DigitalIdeationHSLU/DI8bitbox/documentation/EagleDXFImport.png

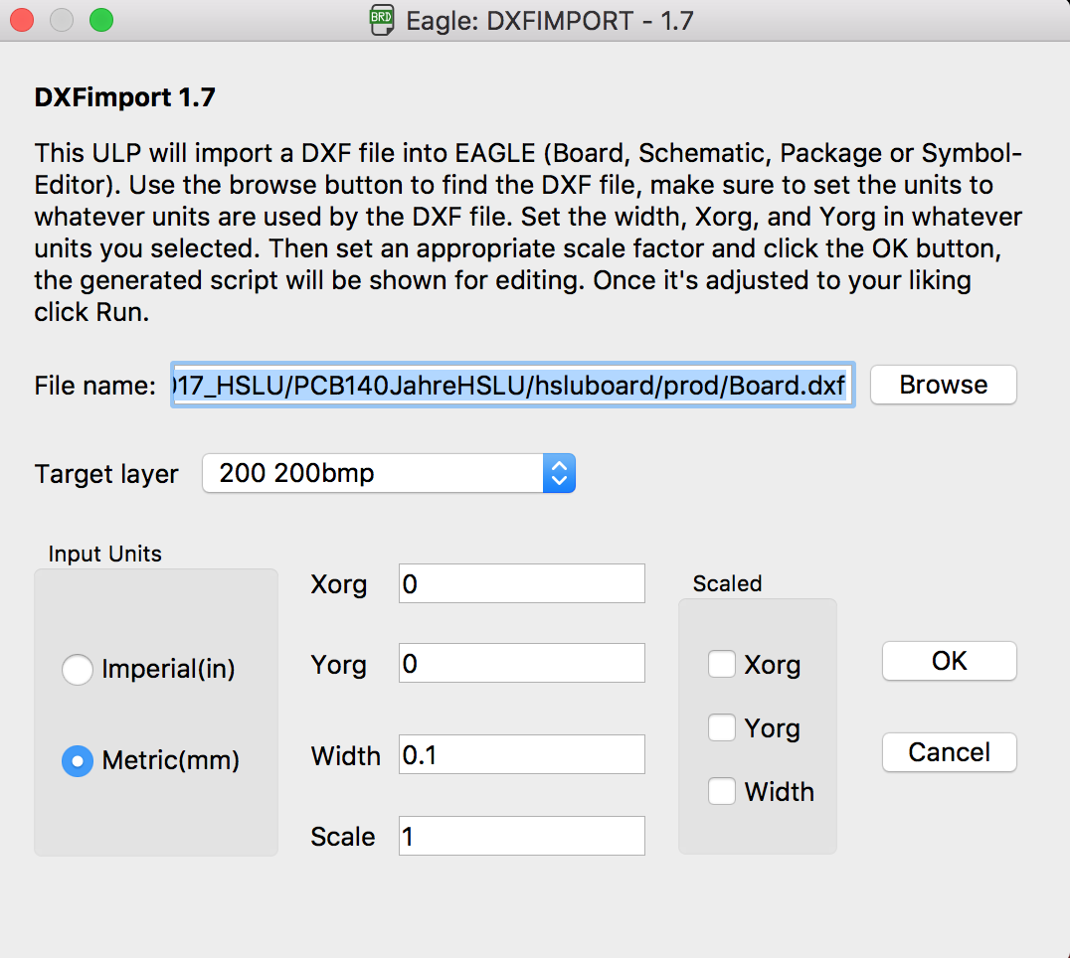
documentation/EagleDXFImport.png
