DigitalIdeationHSLU/DI8bitbox/documentation/EagleUp1.png

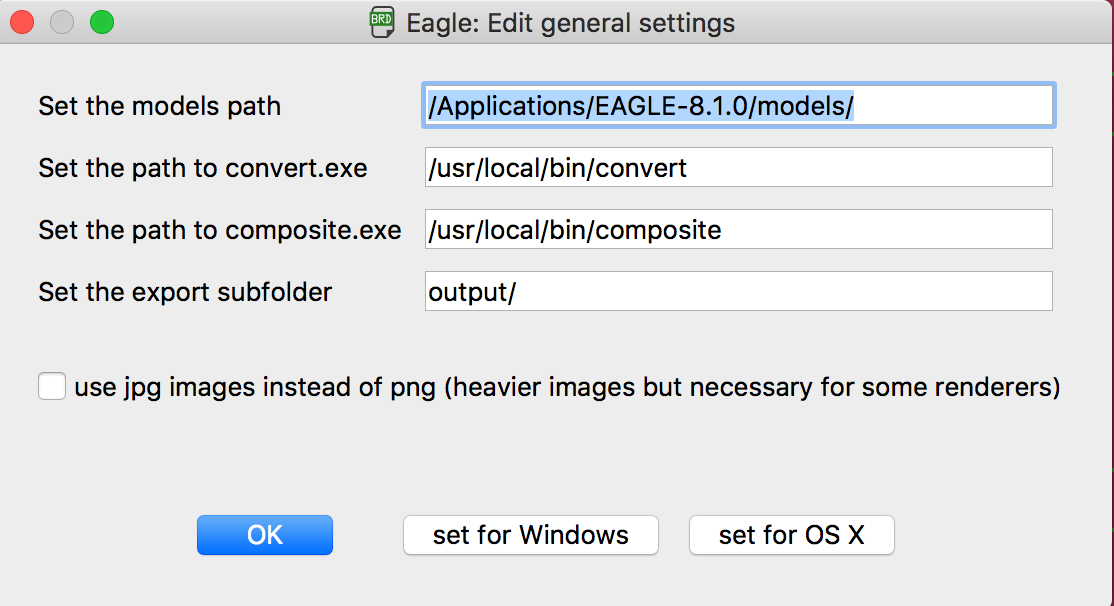
documentation/EagleUp1.png
