DigitalIdeationHSLU/DI8bitbox/documentation/EagleUp2.png

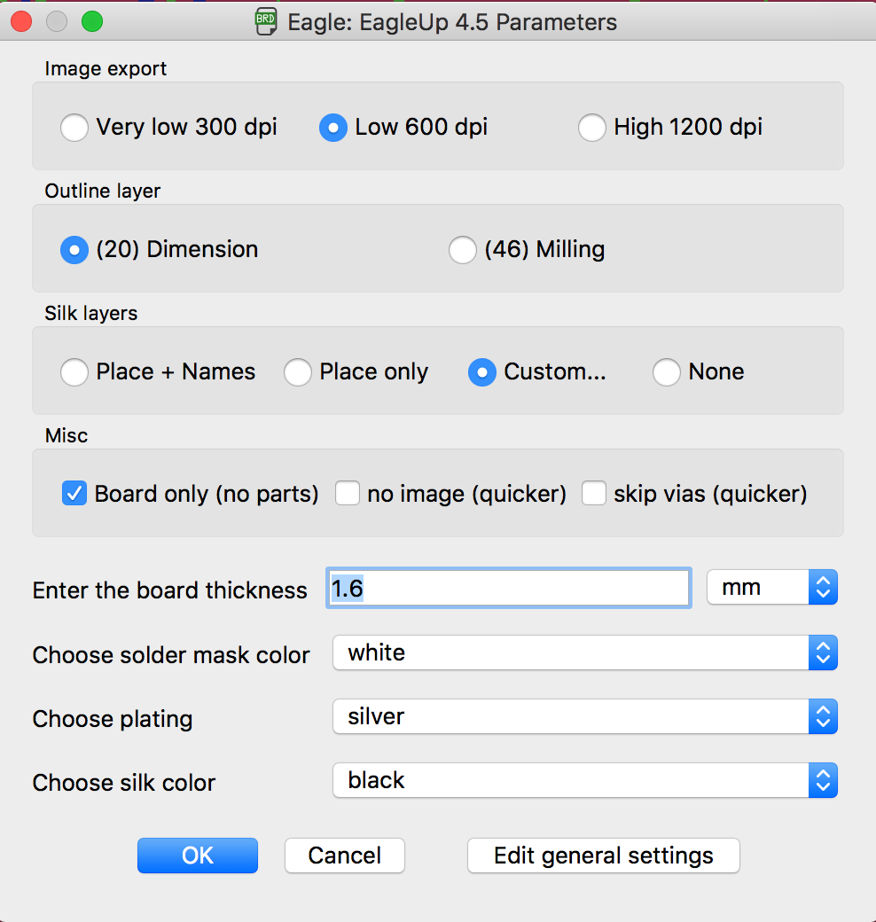
documentation/EagleUp2.png
