DigitalIdeationHSLU/DI8bitbox/documentation/IllustratorDXFexport.png

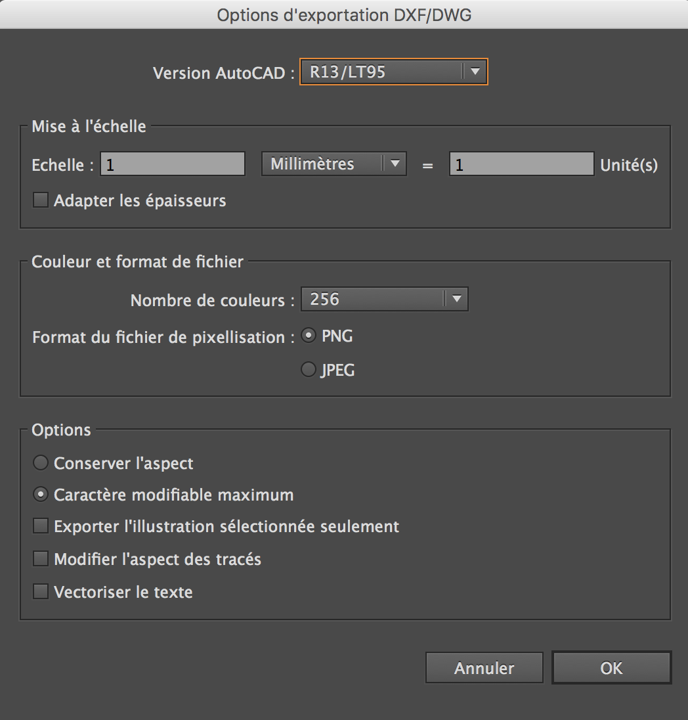
documentation/IllustratorDXFexport.png
