DigitalIdeationHSLU/DI8bitbox/graphics/assets/001-charging-battery.bmp

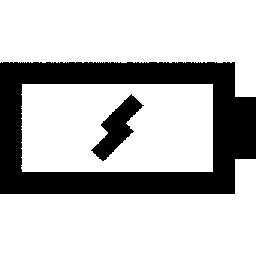
graphics/assets/001-charging-battery.bmp
