DigitalIdeationHSLU/DI8bitbox/graphics/assets/002-speaker.bmp

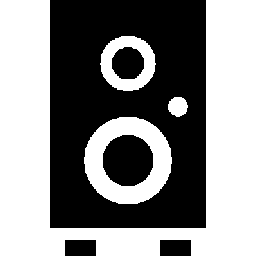
graphics/assets/002-speaker.bmp
