DigitalIdeationHSLU/DI8bitbox/schematics/output/eagleUp_DI8bitbox_board_bottom.png

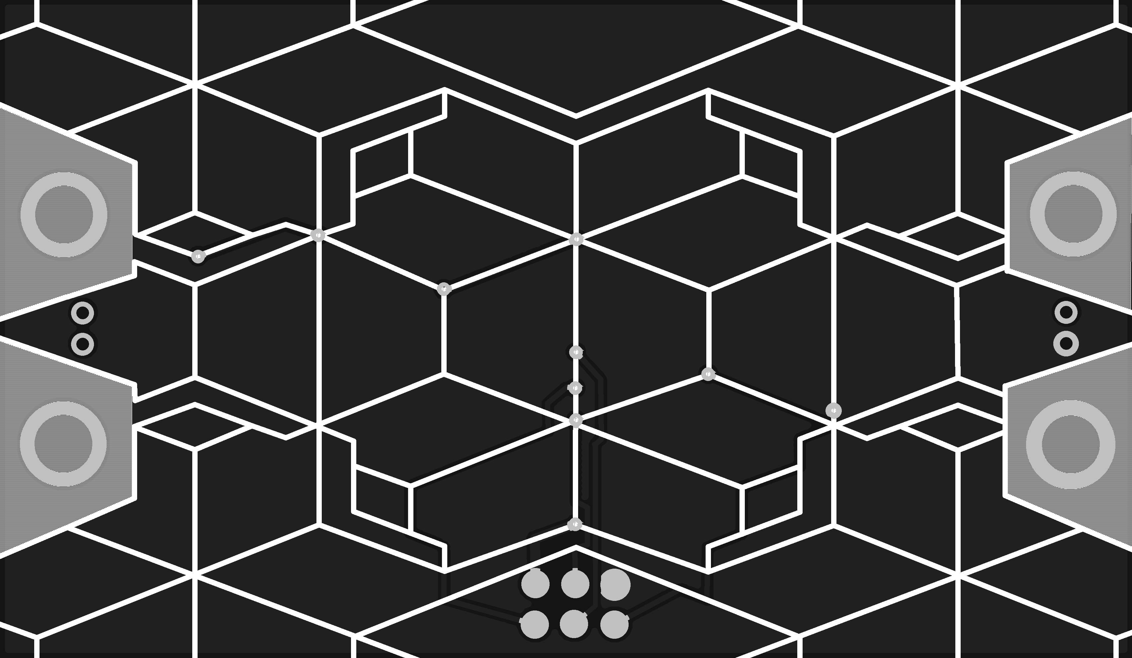
schematics/output/eagleUp_DI8bitbox_board_bottom.png
