DigitalIdeationHSLU/DI8bitbox/schematics/output/eagleUp_DI8bitbox_board_top.png

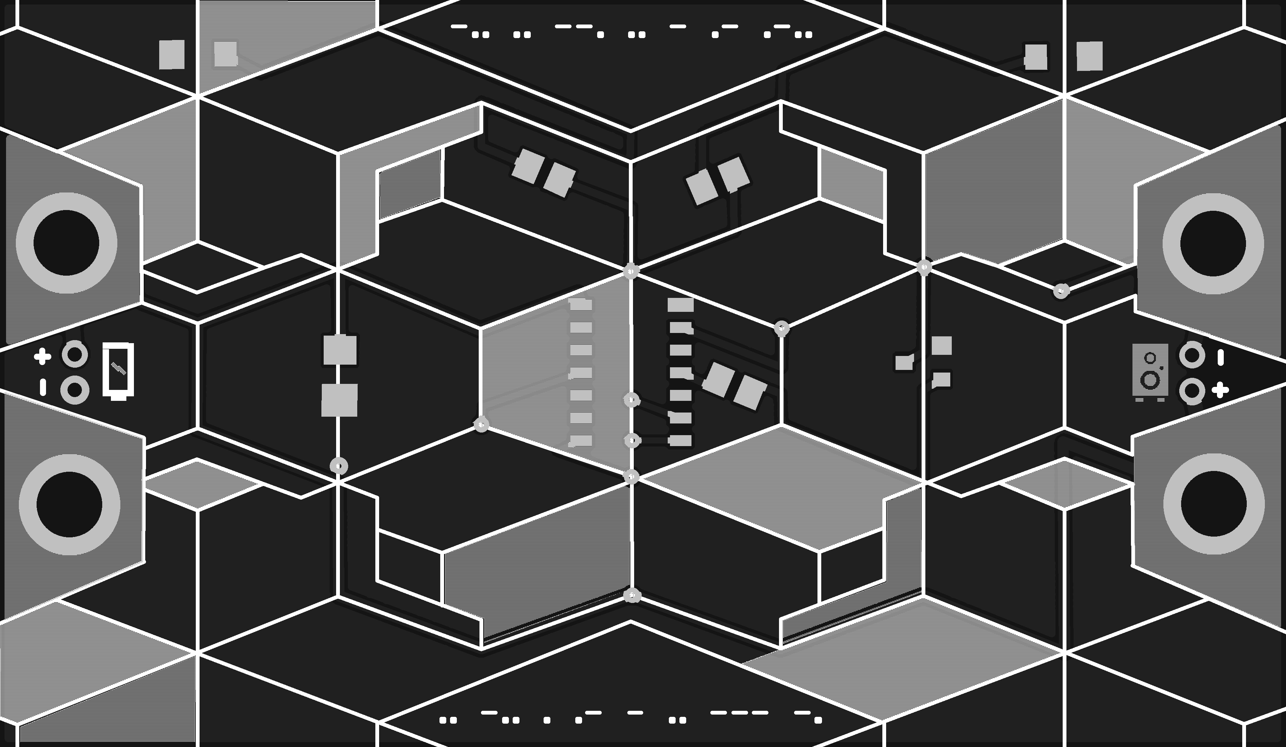
schematics/output/eagleUp_DI8bitbox_board_top.png
