DigitalIdeationHSLU/DI8bitbox/schematics/output/eagleUp_MorseAttiny_board_bottom.png

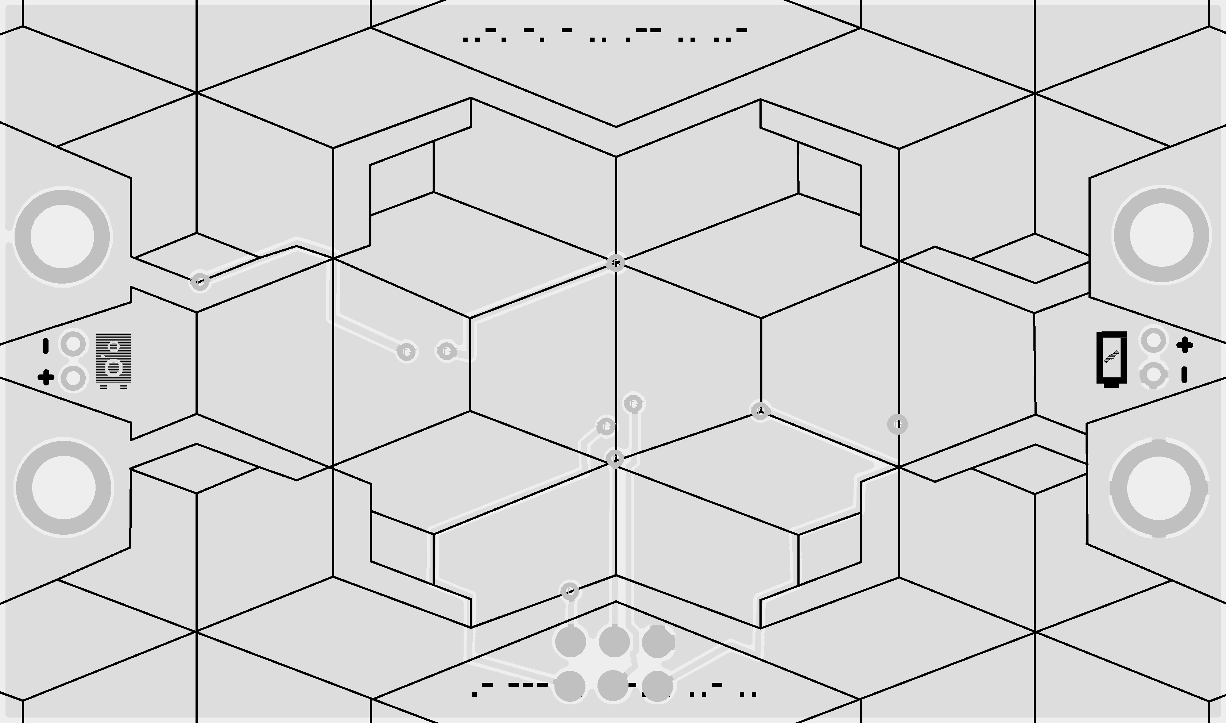
schematics/output/eagleUp_MorseAttiny_board_bottom.png
