DigitalIdeationHSLU/DI8bitbox/schematics/output/eagleUp_MorseAttiny_board_top.png

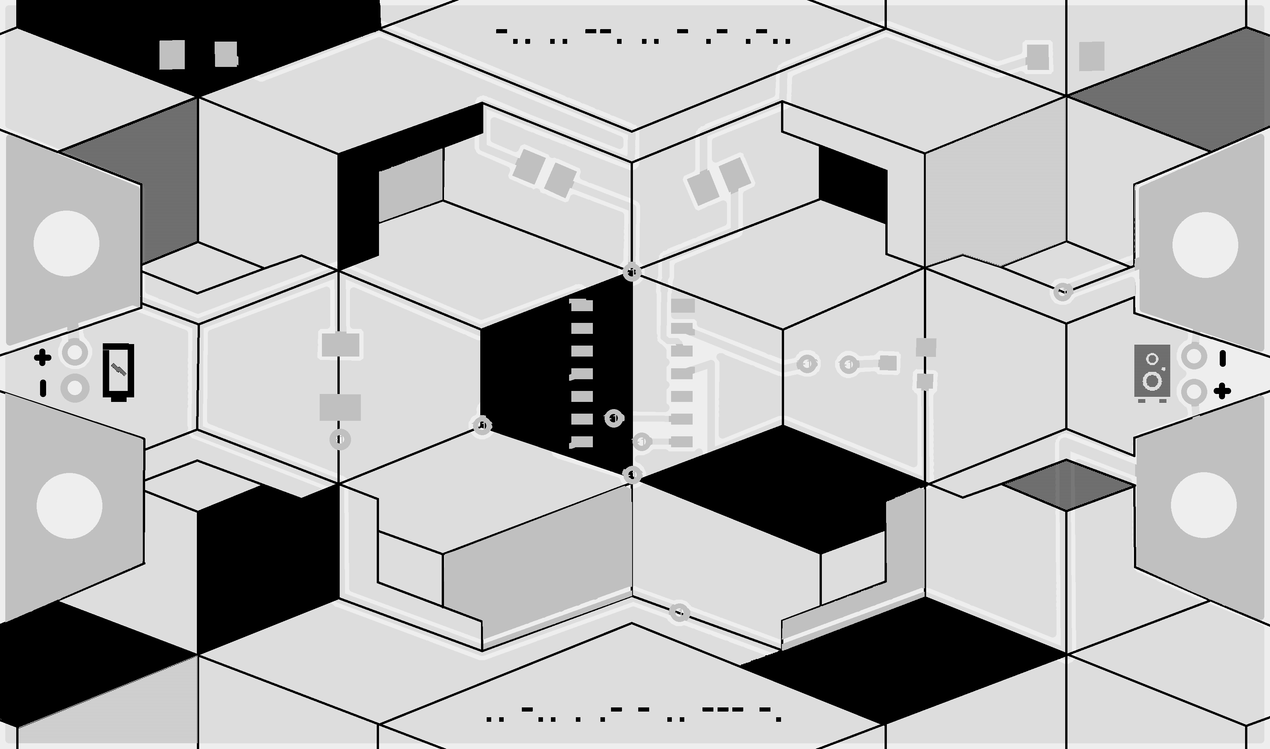
schematics/output/eagleUp_MorseAttiny_board_top.png
